sadekbaroudi/barobord/cases/hipro/bottom-plate.3mf

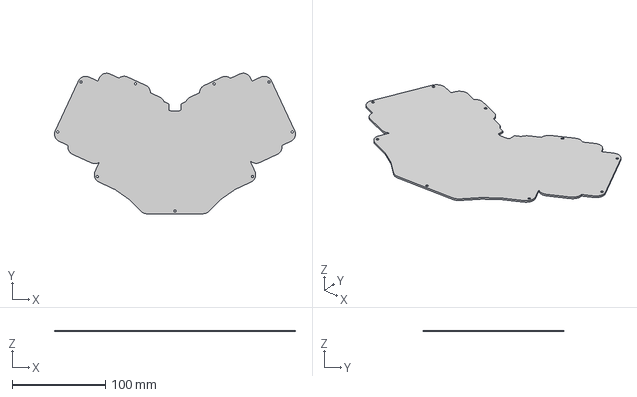
[picture p22: CAD file, 2022-02-24]
cases/hipro/bottom-plate.3mf
258.1 x 150.6 x 1.60 mm
