sadekbaroudi/barobord/cases/OLED-and-encoders-cover.stl

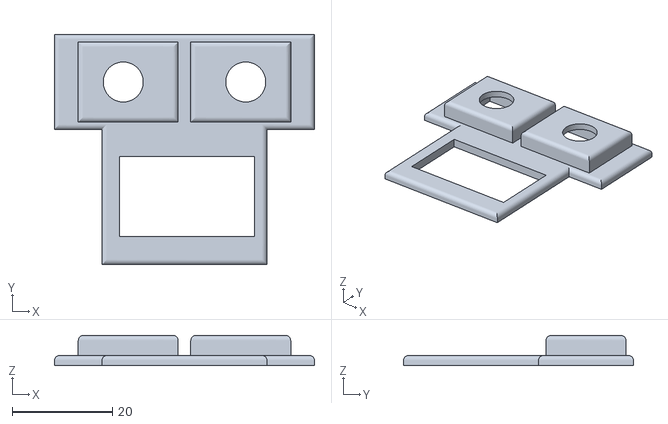
[picture p23: CAD file, 2021-08-10]
cases/OLED-and-encoders-cover.stl
52.0 x 46.0 x 6.00
