sadekbaroudi/barobord/cases/plates/3D/barobord-switchplate-outside-pcb.step

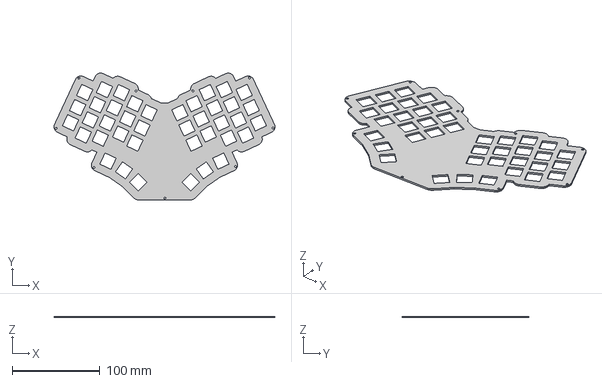
[picture p24: CAD file, 2021-07-30]
cases/plates/3D/barobord-switchplate-outside-pcb.step
251.2 x 144.2 x 1.60 mm
