sadekbaroudi/barobord/cases/covers/ec11-oled-cover.stl

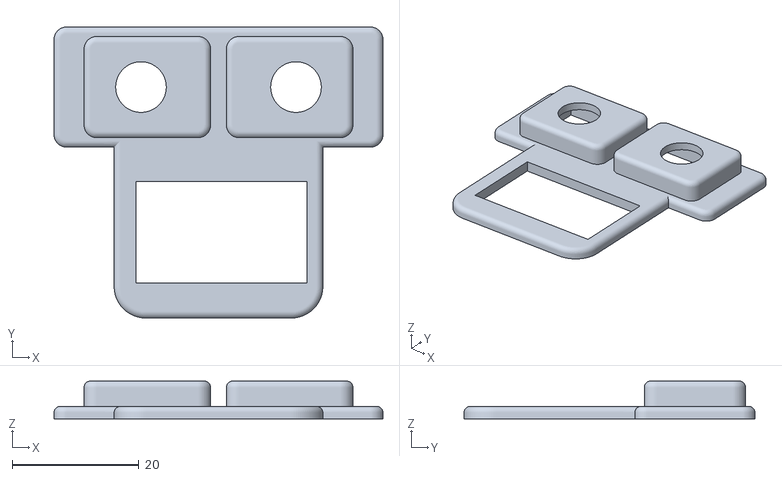
[picture p26: CAD file, 2021-09-09]
cases/covers/ec11-oled-cover.stl
52.0 x 46.0 x 6.00
