sadekbaroudi/barobord/cases/hipro/body-closed-and-raised-center.3mf

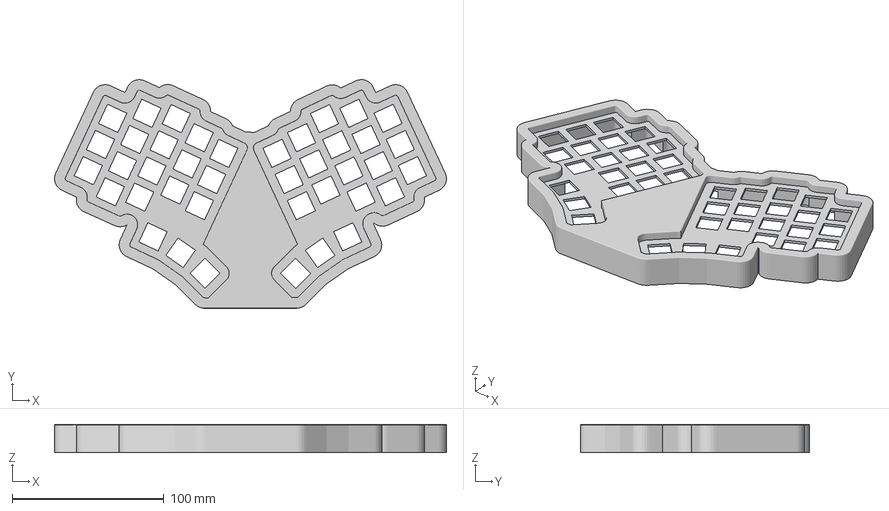
[picture p27: CAD file, 2022-02-24]
cases/hipro/body-closed-and-raised-center.3mf
258.1 x 150.6 x 18.6 mm
