sadekbaroudi/barobord/cases/plates/3D/barobord-bottom-plate-outside-pcb.step

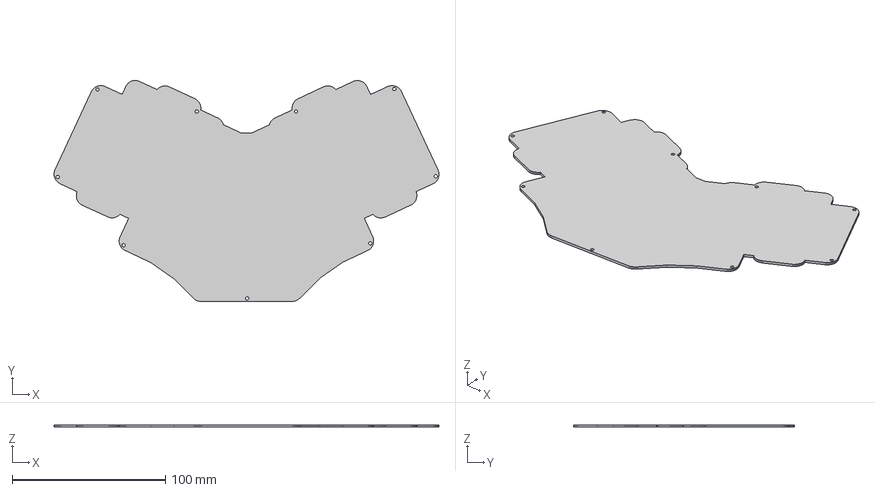
[picture p28: CAD file, 2021-07-30]
cases/plates/3D/barobord-bottom-plate-outside-pcb.step
251.2 x 144.2 x 1.60 mm
