sadekbaroudi/barobord/cases/plates/svg-dxf/bottom-plate-outside-pcb.dxf

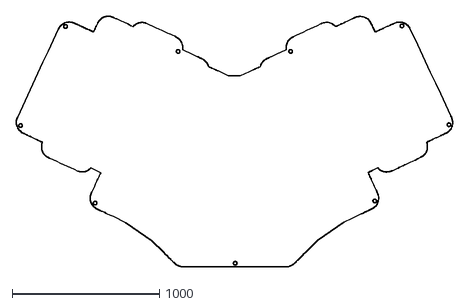
[picture p29: CAD file, 2021-07-30]
cases/plates/svg-dxf/bottom-plate-outside-pcb.dxf
2965.6 x 1702.8
