sadekbaroudi/barobord/cases/sandwich/switchplate-case-2rotary-and-pimoroni.stl

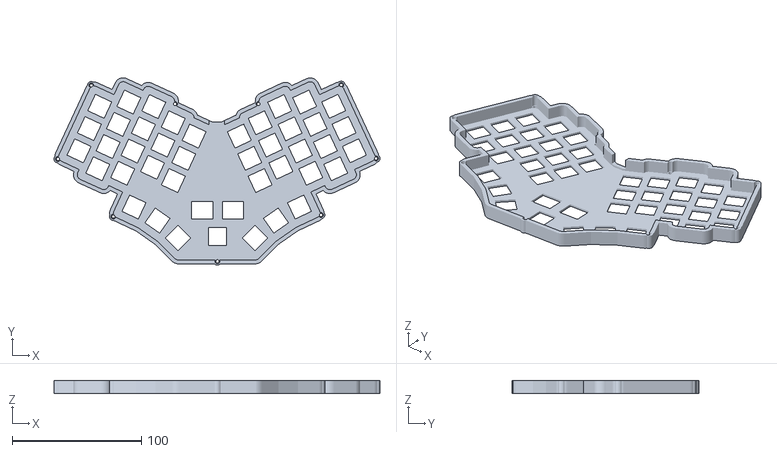
[picture p30: CAD file, 2021-08-28]
cases/sandwich/switchplate-case-2rotary-and-pimoroni.stl
252.6 x 145.2 x 10.0
