sadekbaroudi/barobord/cases/sandwich/switchplate-negative-slope.stl

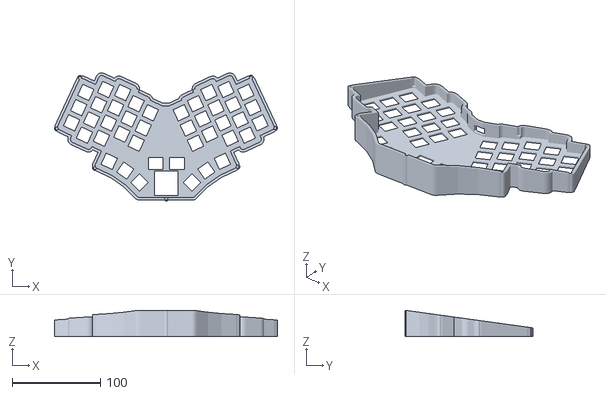
[picture p31: CAD file, 2021-08-06]
cases/sandwich/switchplate-negative-slope.stl
252.6 x 145.2 x 30.0
