sadekbaroudi/barobord/cases/sandwich/bottom-negative-slope.stl

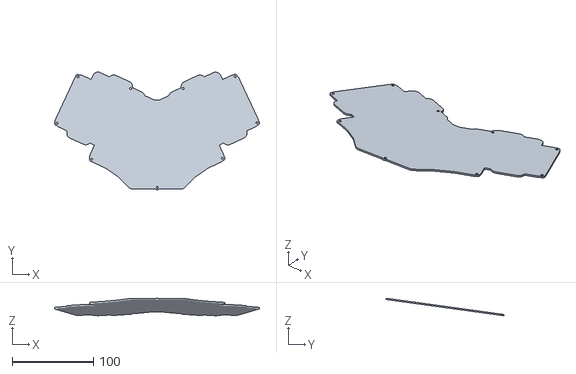
[picture p32: CAD file, 2021-08-06]
cases/sandwich/bottom-negative-slope.stl
252.6 x 145.2 x 21.6
